neighborhood-watch-alarm/nwa/site/frontend/src/Images/alarmsystem-basics.png

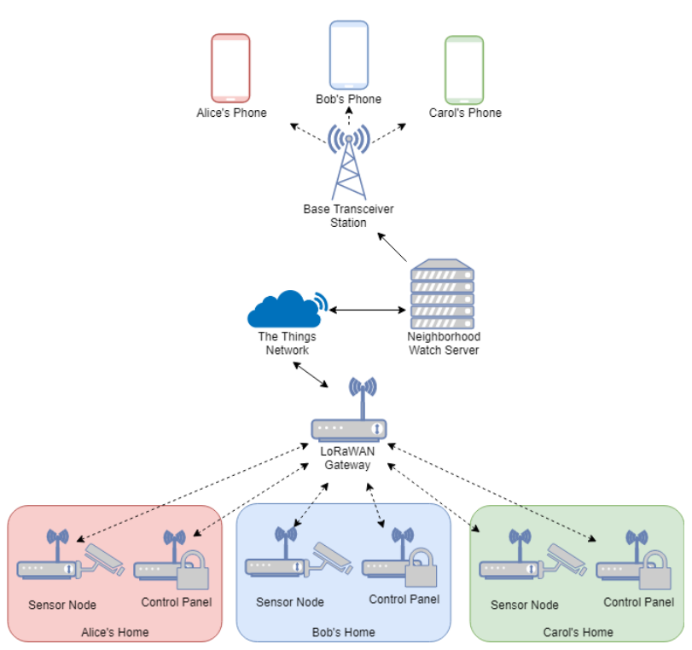
site/frontend/src/Images/alarmsystem-basics.png
