neighborhood-watch-alarm/nwa/site/frontend/src/Images/alarmWelcome-preview.png

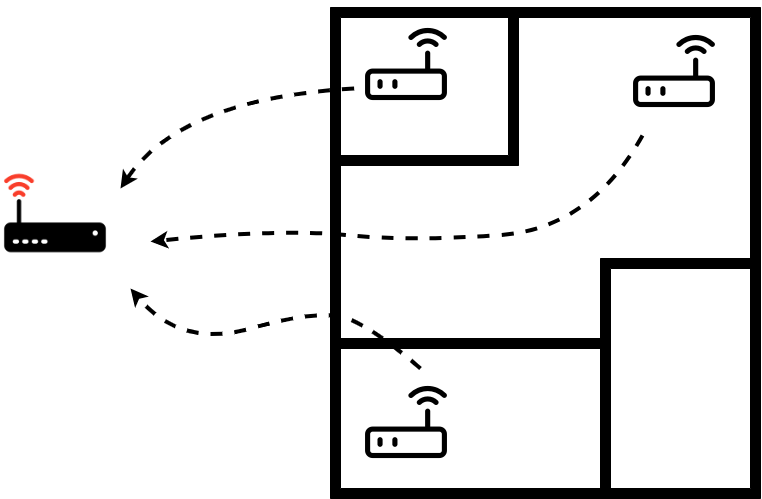
site/frontend/src/Images/alarmWelcome-preview.png
