neighborhood-watch-alarm/nwa/site/frontend/src/Images/arduino-serial.png

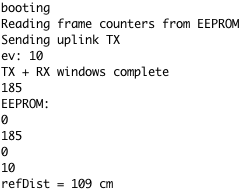
site/frontend/src/Images/arduino-serial.png
