neighborhood-watch-alarm/nwa/site/frontend/src/Images/database.png

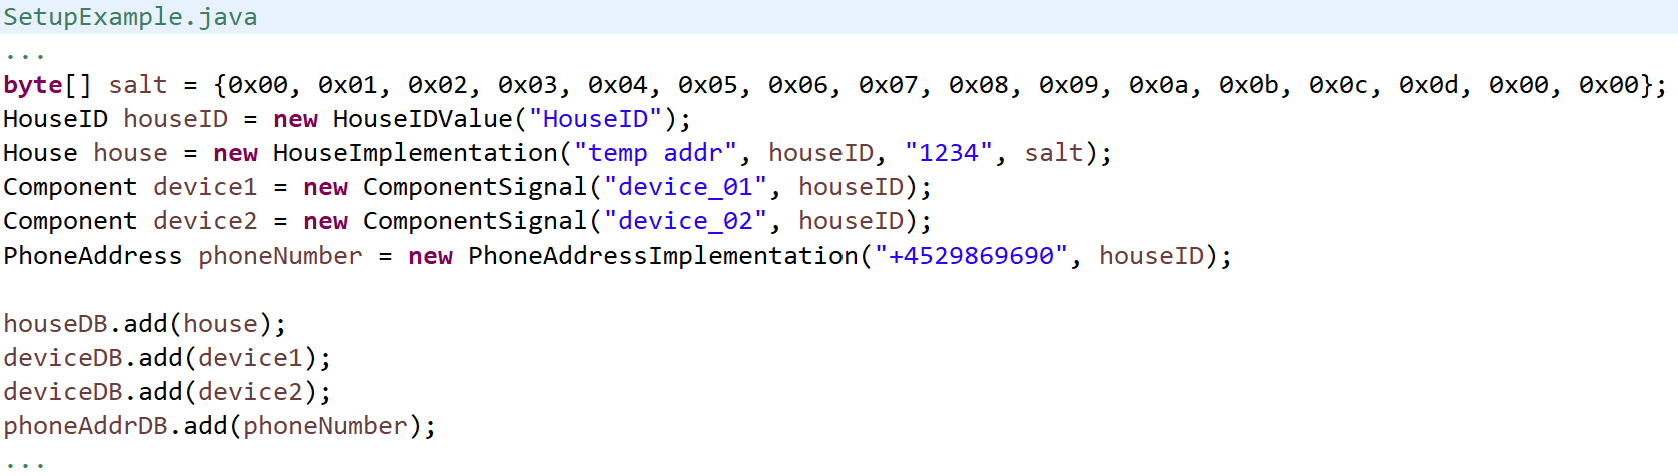
site/frontend/src/Images/database.png
