neighborhood-watch-alarm/nwa/site/frontend/src/Images/Fritzing/Images/breadboard.png

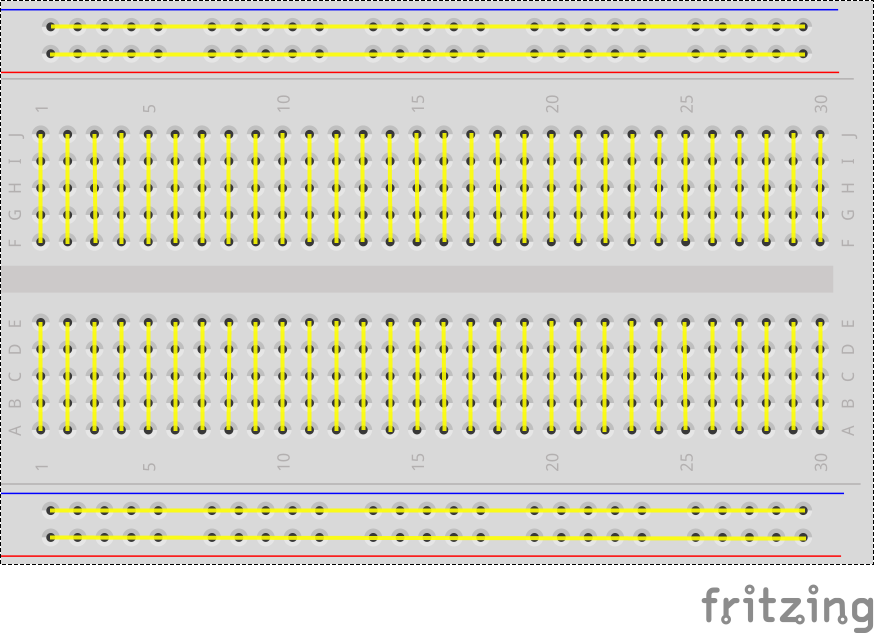
site/frontend/src/Images/Fritzing/Images/breadboard.png
