neighborhood-watch-alarm/nwa/site/frontend/src/Images/Fritzing/Images/ControlBasic.png

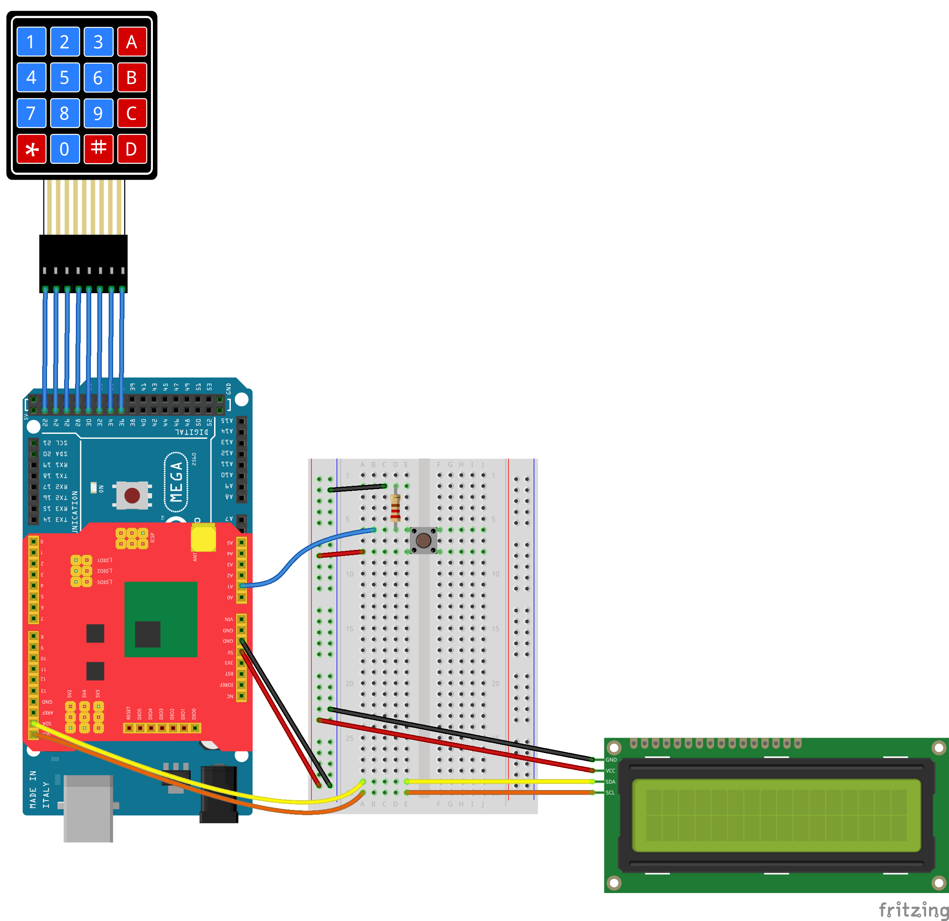
site/frontend/src/Images/Fritzing/Images/ControlBasic.png
