neighborhood-watch-alarm/nwa/site/frontend/src/Images/Fritzing/Images/ControlBasic_breadboard.png

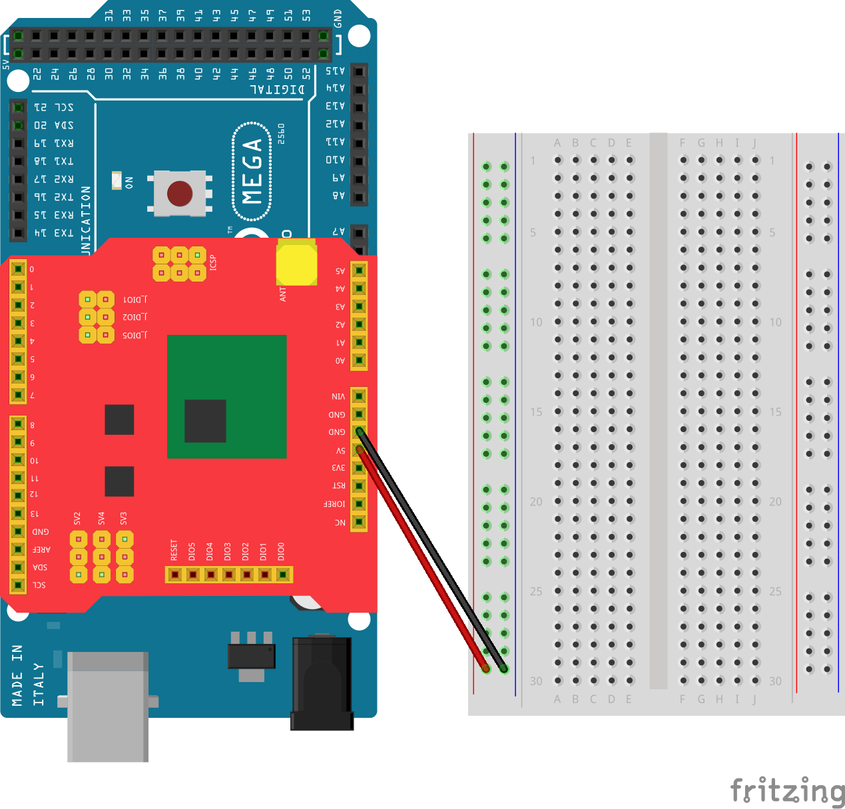
site/frontend/src/Images/Fritzing/Images/ControlBasic_breadboard.png
