neighborhood-watch-alarm/nwa/site/frontend/src/Images/Fritzing/Images/ControlBasic_panic.png

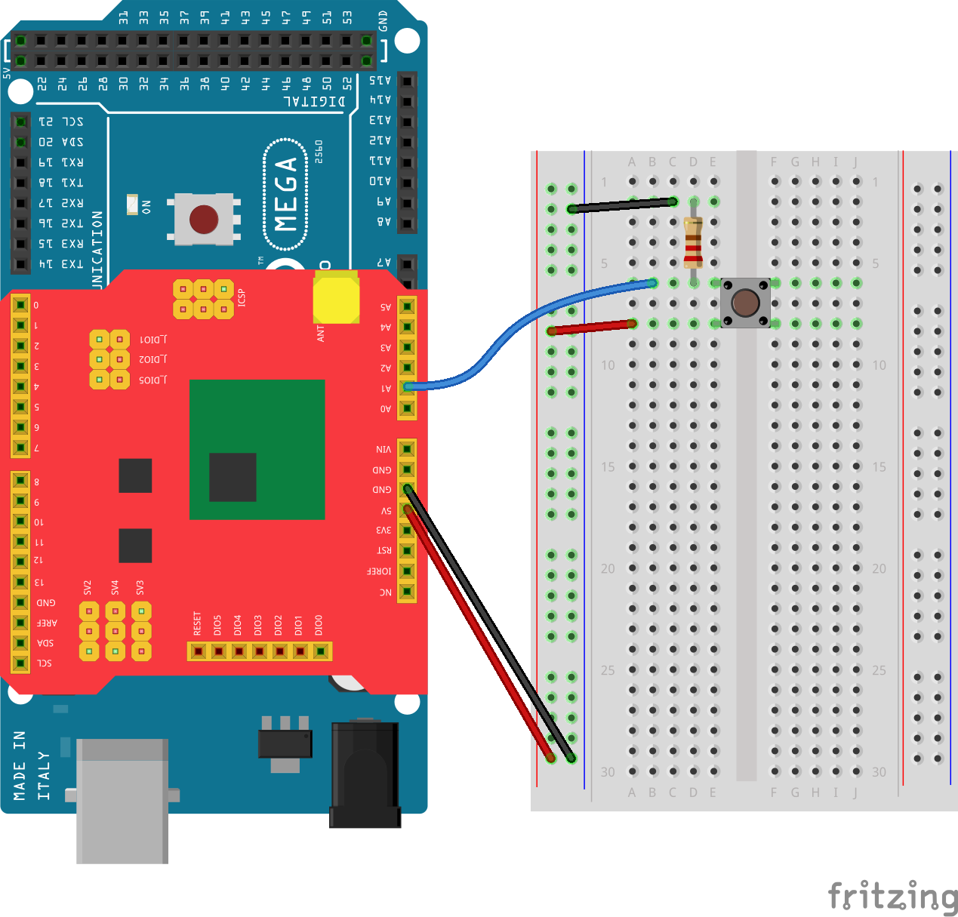
site/frontend/src/Images/Fritzing/Images/ControlBasic_panic.png
