neighborhood-watch-alarm/nwa/site/frontend/src/Images/Fritzing/Images/ControlBasic_shield.png

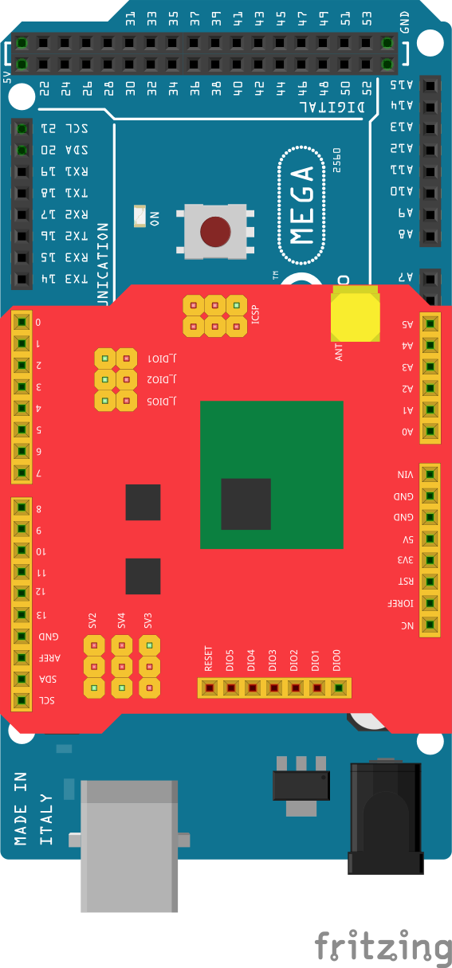
site/frontend/src/Images/Fritzing/Images/ControlBasic_shield.png
