neighborhood-watch-alarm/nwa/site/frontend/src/Images/Fritzing/Images/ControlLIDAR.png

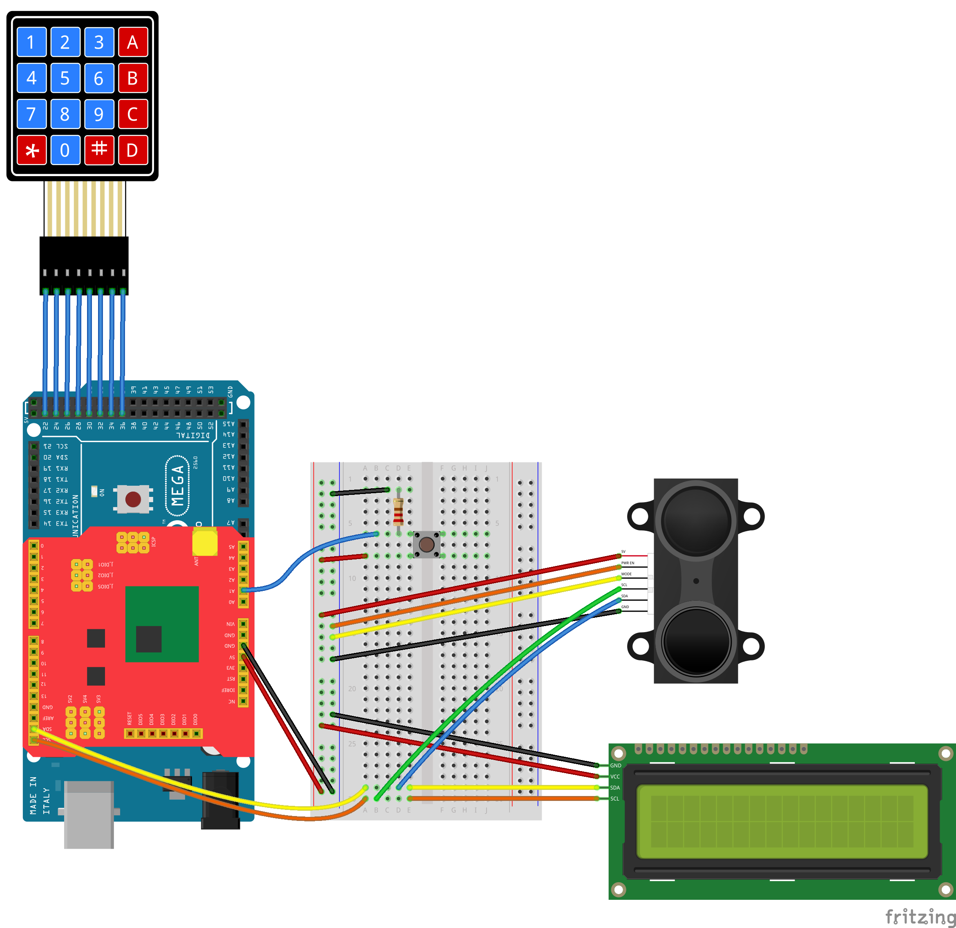
site/frontend/src/Images/Fritzing/Images/ControlLIDAR.png
