neighborhood-watch-alarm/nwa/site/frontend/src/Images/Fritzing/Images/NodeBasic.png

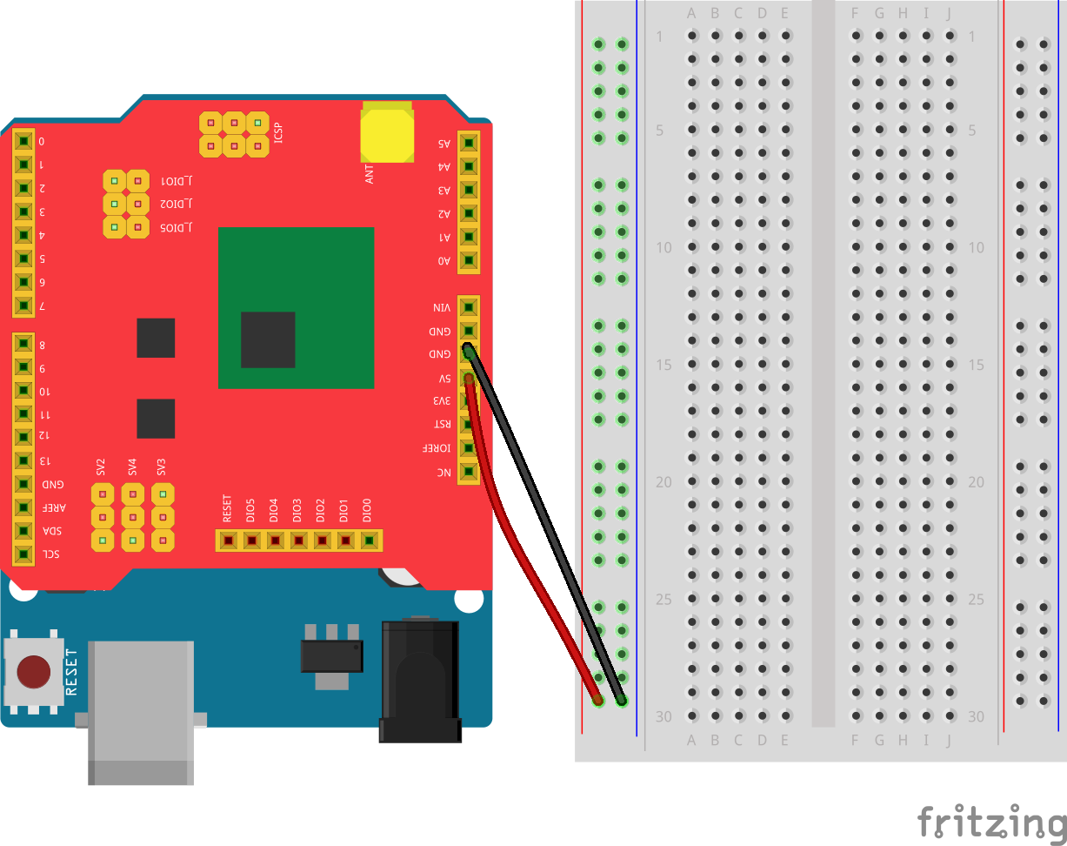
site/frontend/src/Images/Fritzing/Images/NodeBasic.png
