neighborhood-watch-alarm/nwa/site/frontend/src/Images/Fritzing/Images/NodePIR.png

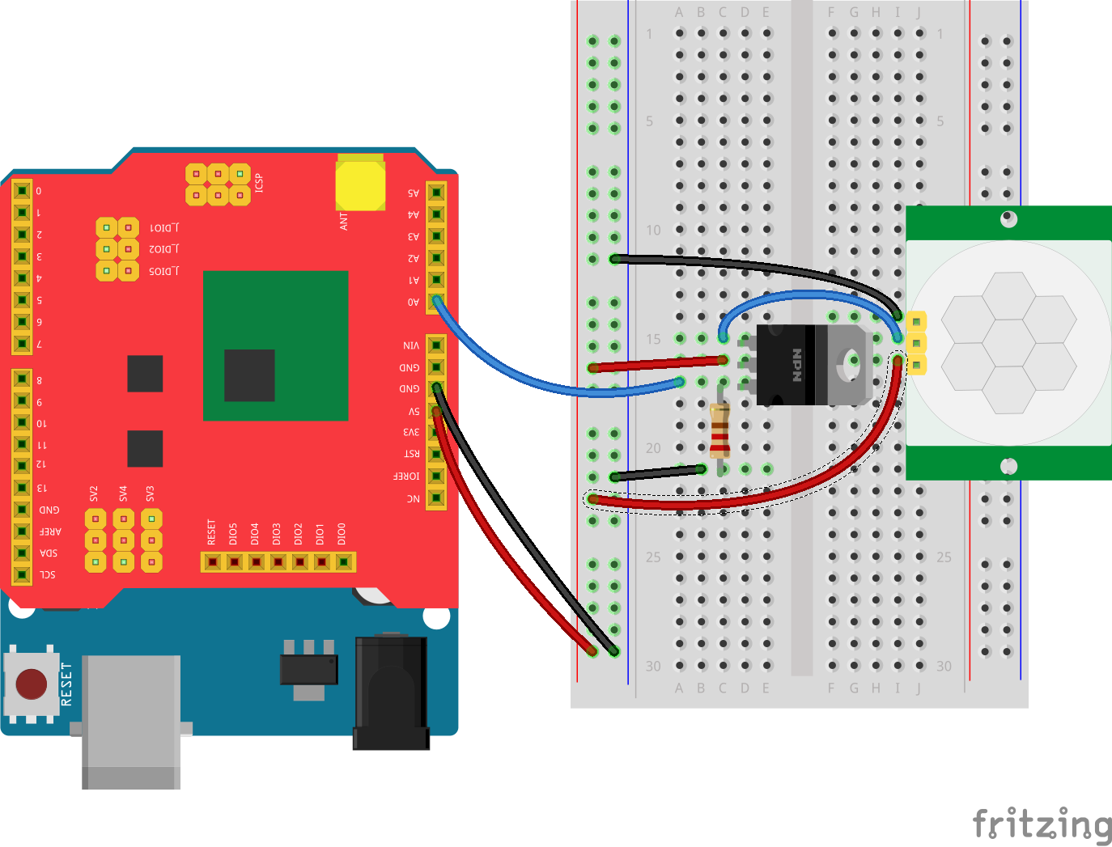
site/frontend/src/Images/Fritzing/Images/NodePIR.png
