neighborhood-watch-alarm/nwa/site/frontend/src/Images/Fritzing/Images/NodeUS.png

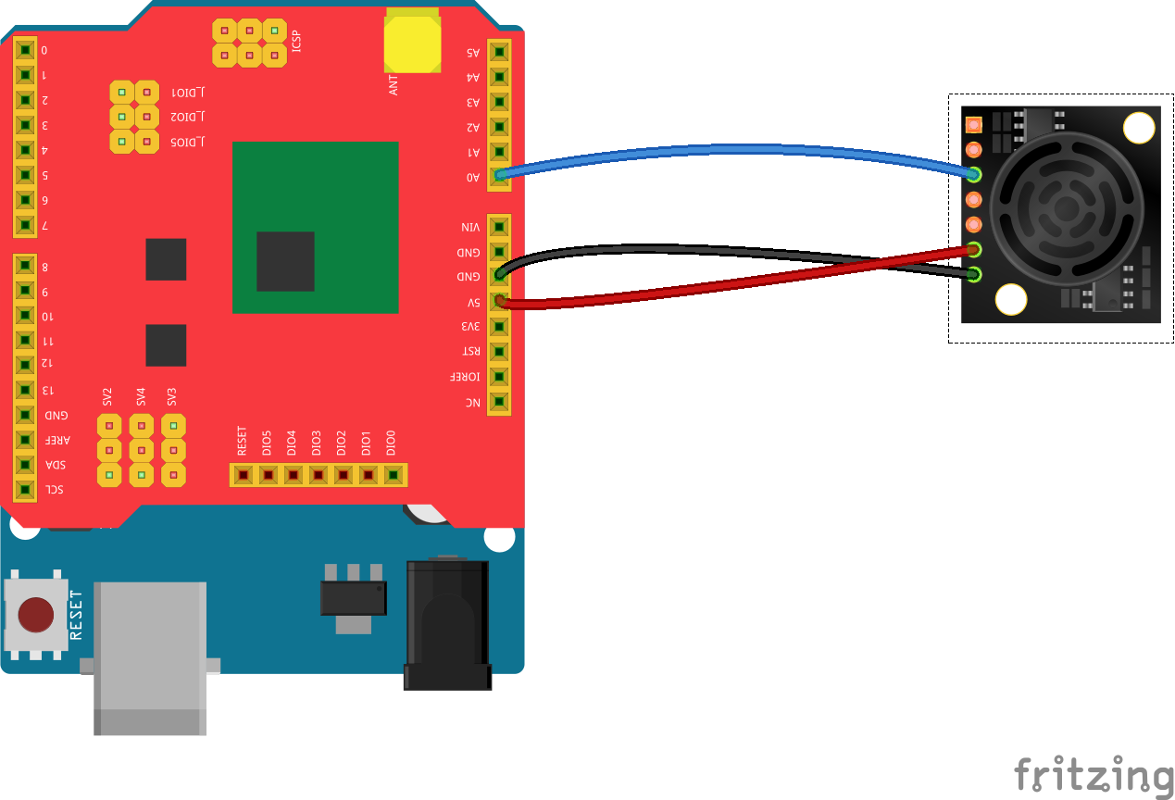
site/frontend/src/Images/Fritzing/Images/NodeUS.png
