neighborhood-watch-alarm/nwa/site/frontend/src/Images/mainMethod.png

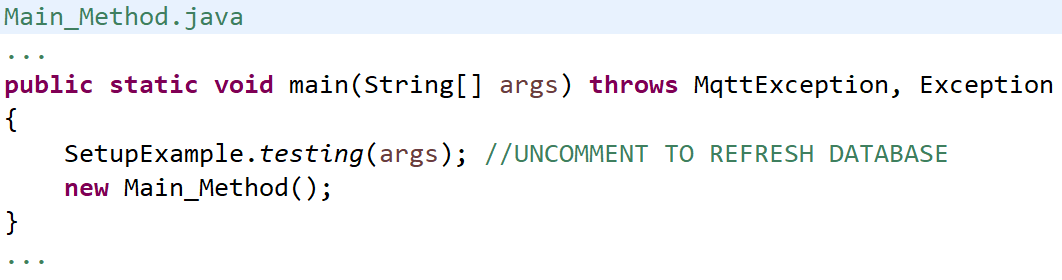
site/frontend/src/Images/mainMethod.png
