neighborhood-watch-alarm/nwa/site/frontend/src/Images/rasImager.png

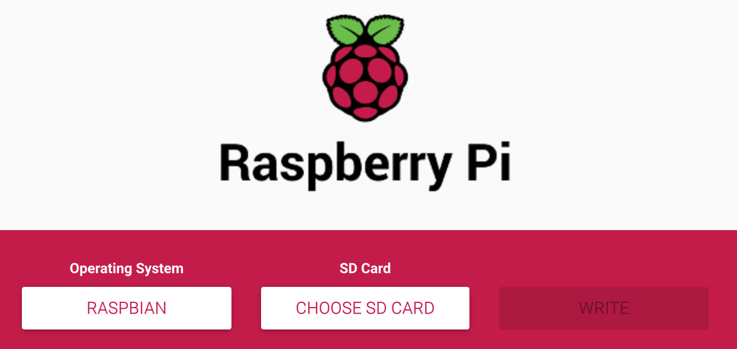
site/frontend/src/Images/rasImager.png
