neighborhood-watch-alarm/nwa/site/frontend/src/Images/winSCP.png

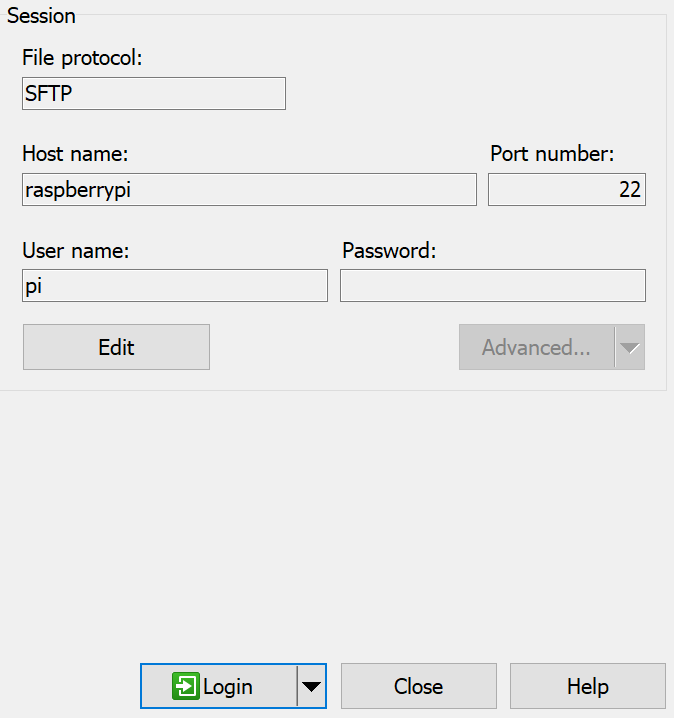
site/frontend/src/Images/winSCP.png
