neighborhood-watch-alarm/nwa/site/frontend/src/Images/arduino-verify.png

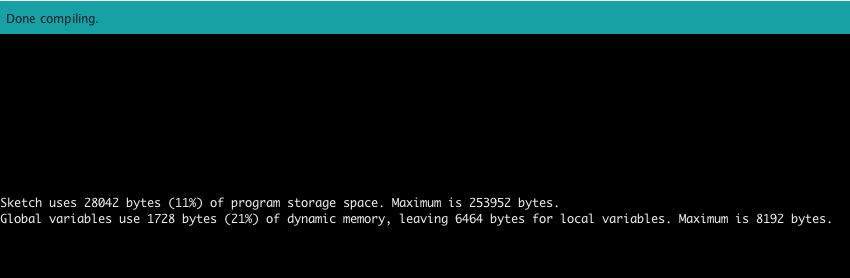
site/frontend/src/Images/arduino-verify.png
